ThomasVanNuffel/Iron-Solo-Synthesizer/Practise Enterprise 1/Drawings/Balance amplifier.tif

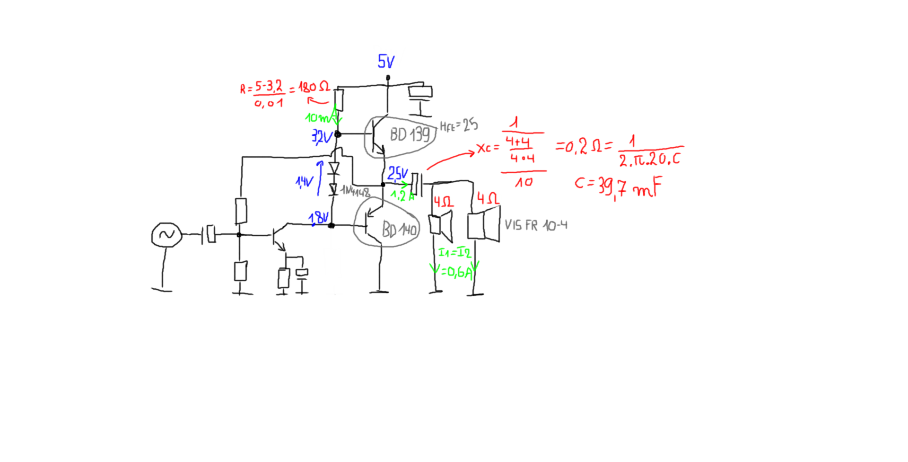
Practise Enterprise 1/Drawings/Balance amplifier.tif
