ThomasVanNuffel/Iron-Solo-Synthesizer/Practise Enterprise 1/Drawings/try.png

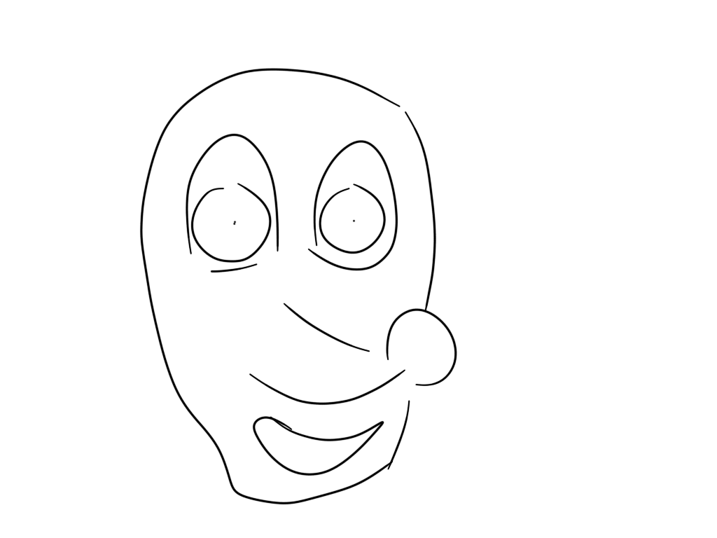
Practise Enterprise 1/Drawings/try.png
