ThomasVanNuffel/Iron-Solo-Synthesizer/Practise Enterprise 1/PCB/Nieuwe map/Envelope board.png

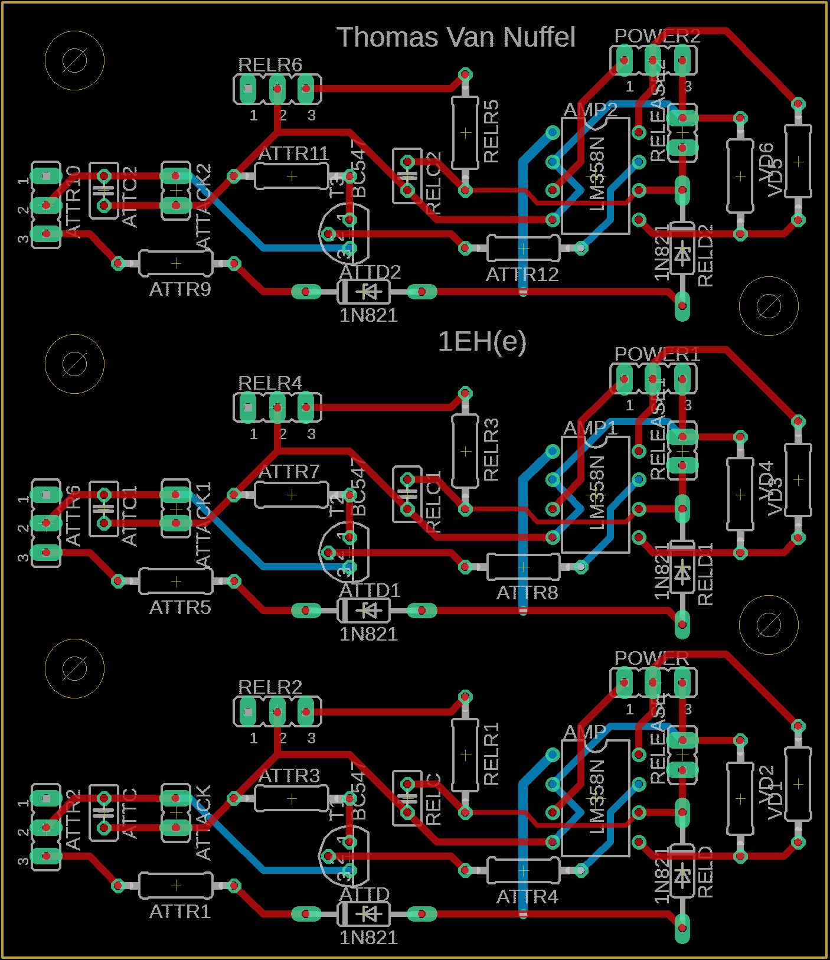
Practise Enterprise 1/PCB/Nieuwe map/Envelope board.png
