ThomasVanNuffel/Iron-Solo-Synthesizer/Practise Enterprise 1/PCB/Nieuwe map/Filter board.png

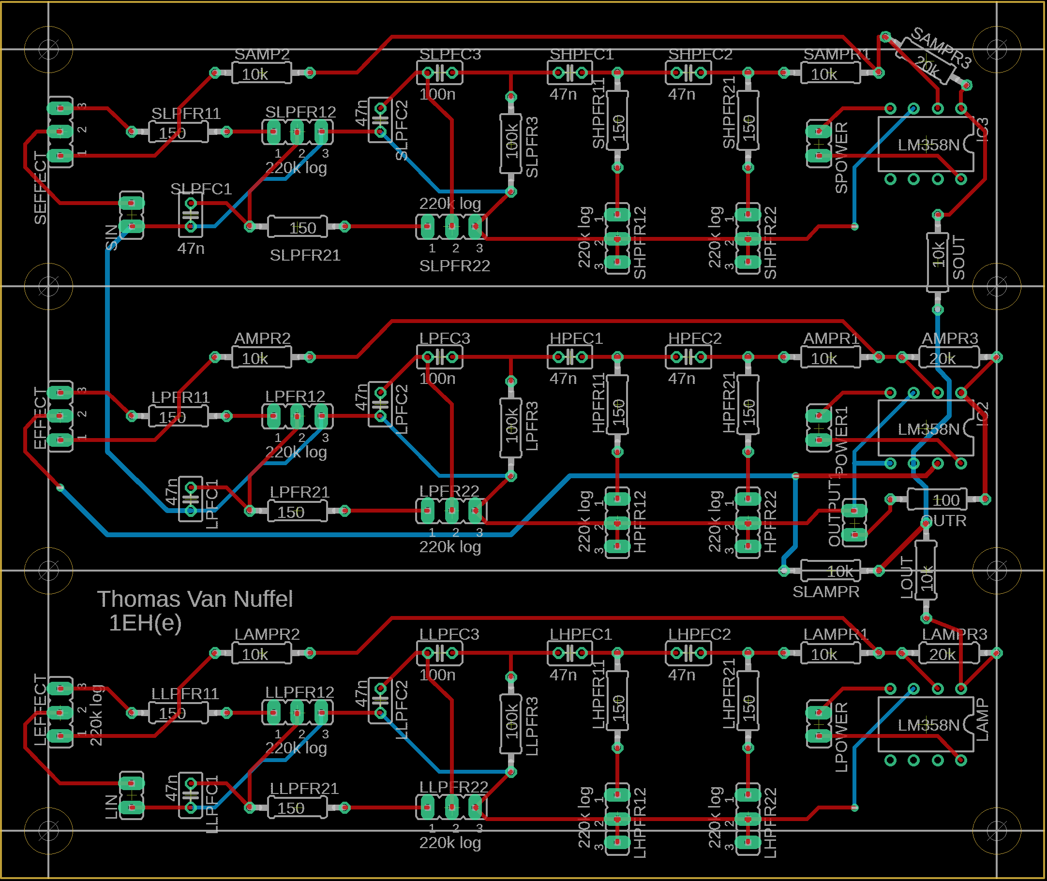
Practise Enterprise 1/PCB/Nieuwe map/Filter board.png
