ThomasVanNuffel/Iron-Solo-Synthesizer/Practise Enterprise 1/Design/EC11_rotary_encoder_knob.stp

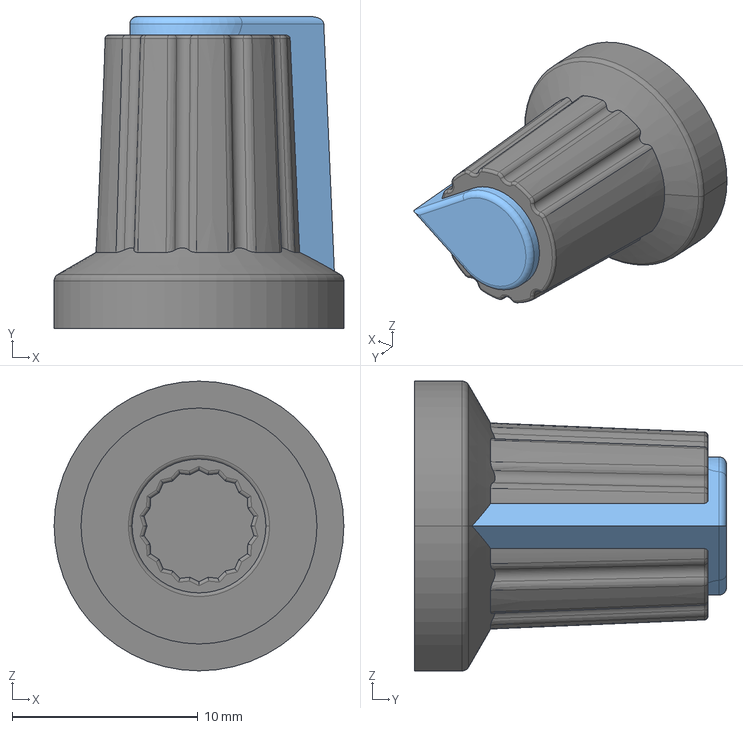
[picture p28: CAD file, 2021-11-29]
Practise Enterprise 1/Design/EC11_rotary_encoder_knob.stp
15.6 x 16.8 x 15.6 mm
