ThomasVanNuffel/Iron-Solo-Synthesizer/Practise Enterprise 1/Design/ground panel.SLDPRT

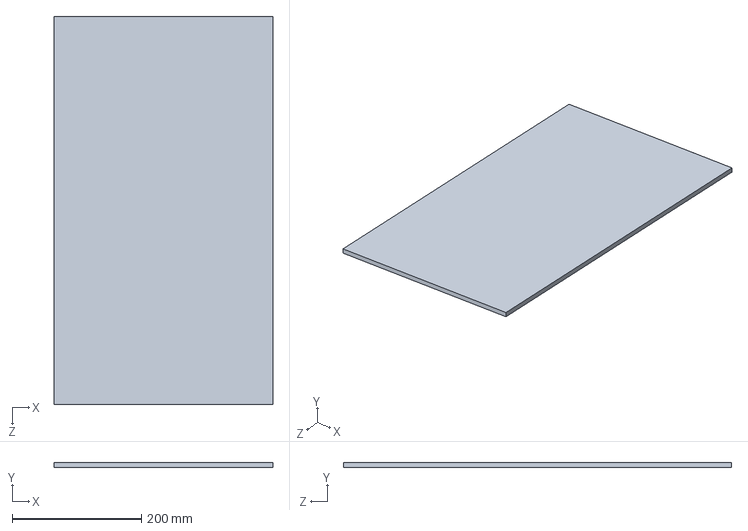
[picture p29: CAD file, 2021-11-29]
Practise Enterprise 1/Design/ground panel.SLDPRT
338.0 x 8.00 x 600.0 mm
