ThomasVanNuffel/Iron-Solo-Synthesizer/Practise Enterprise 1/Design/Part20.SLDPRT

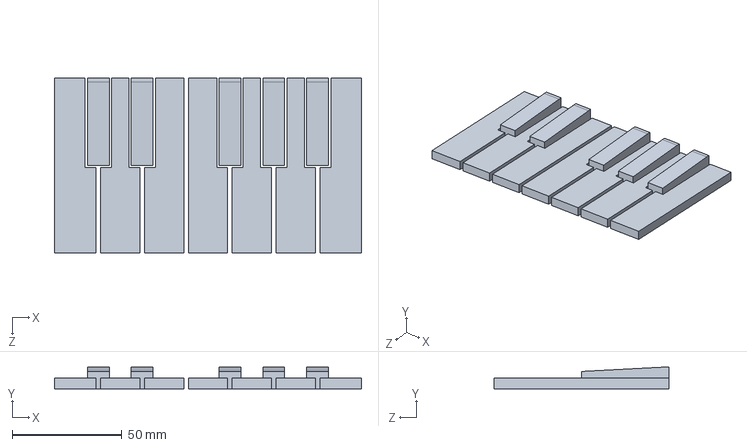
[picture p30: CAD file, 2021-11-29]
Practise Enterprise 1/Design/Part20.SLDPRT
140.0 x 10.0 x 80.0 mm
