ThomasVanNuffel/Iron-Solo-Synthesizer/Practise Enterprise 1/Design/RS-209-gold.step

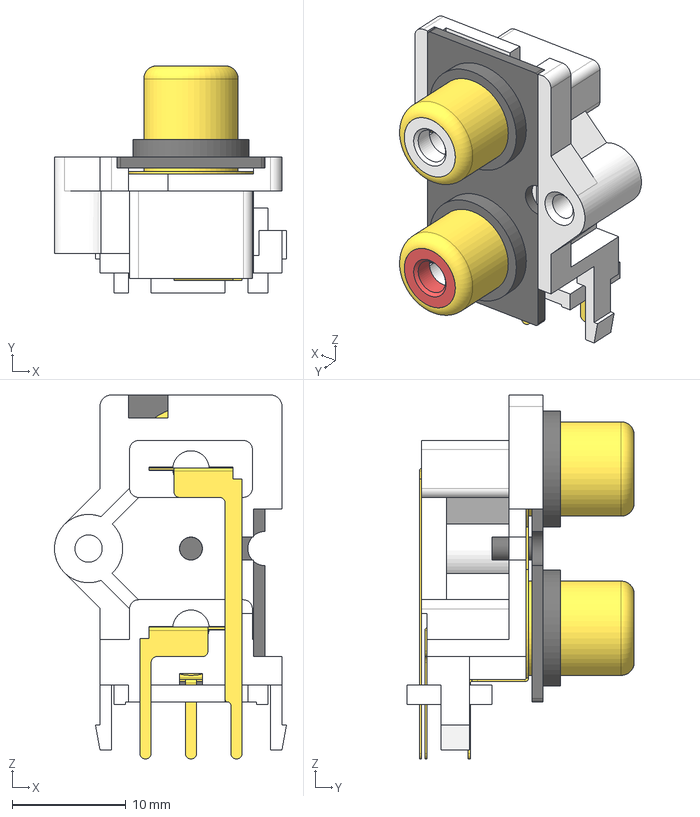
[picture p31: CAD file, 2021-11-29]
Practise Enterprise 1/Design/RS-209-gold.step
20.4 x 20.0 x 32.0 mm
