ThomasVanNuffel/Iron-Solo-Synthesizer/Practise Enterprise 1/Design/EG1249.step

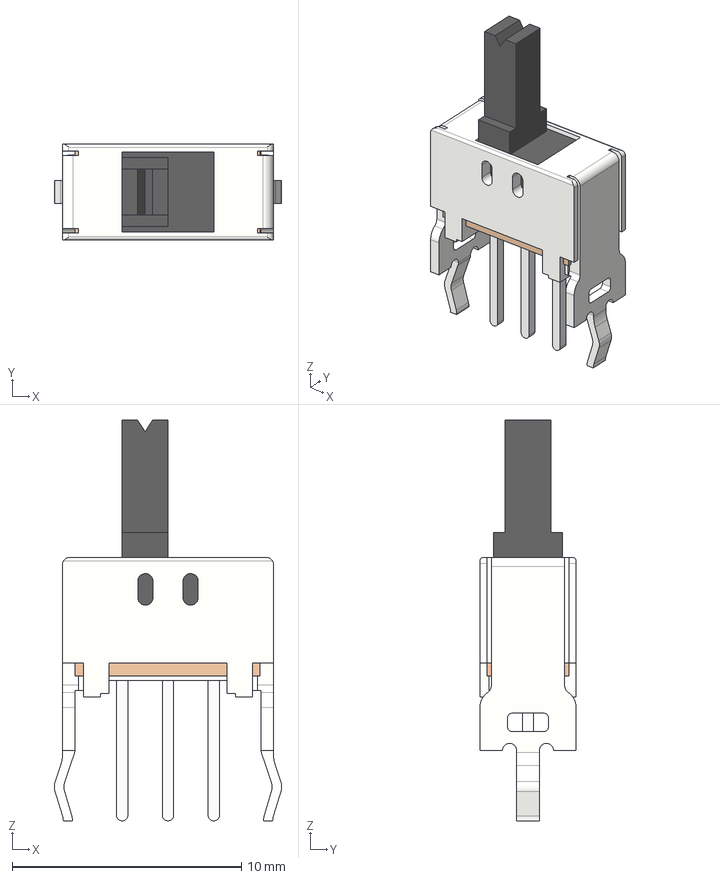
[picture p32: CAD file, 2021-11-29]
Practise Enterprise 1/Design/EG1249.step
9.93 x 4.20 x 17.5 mm
