ThomasVanNuffel/Iron-Solo-Synthesizer/Practise Enterprise 1/Design/front panel.SLDPRT

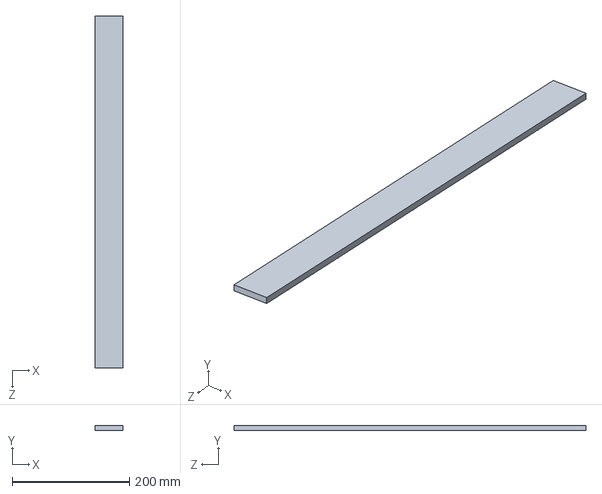
[picture p33: CAD file, 2021-11-29]
Practise Enterprise 1/Design/front panel.SLDPRT
48.0 x 8.00 x 600.0 mm
