ThomasVanNuffel/Iron-Solo-Synthesizer/Practise Enterprise 1/Design/ST-215N-01.step

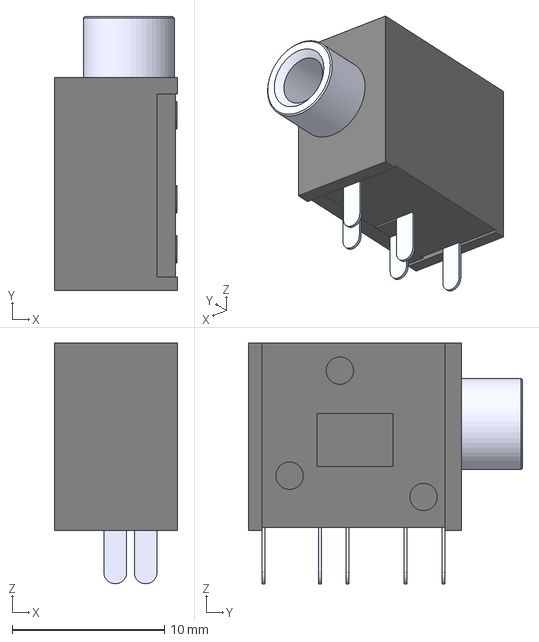
[picture p34: CAD file, 2021-11-29]
Practise Enterprise 1/Design/ST-215N-01.step
8.10 x 18.0 x 15.8 mm
