ThomasVanNuffel/Iron-Solo-Synthesizer/Practise Enterprise 1/Design/back panel.SLDPRT

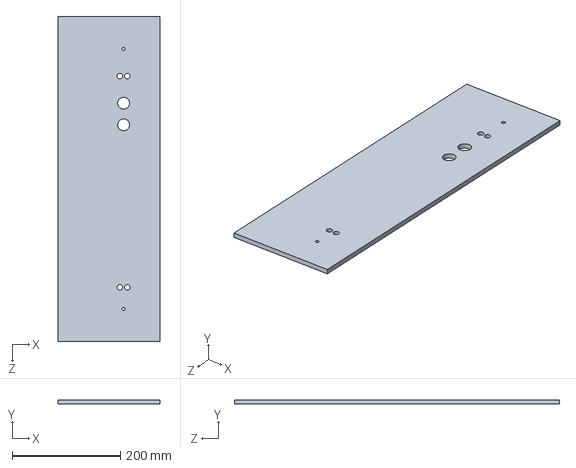
[picture p35: CAD file, 2021-11-29]
Practise Enterprise 1/Design/back panel.SLDPRT
188.0 x 8.00 x 600.0 mm
