ThomasVanNuffel/Iron-Solo-Synthesizer/Practise Enterprise 1/Design/bigpotje.STEP

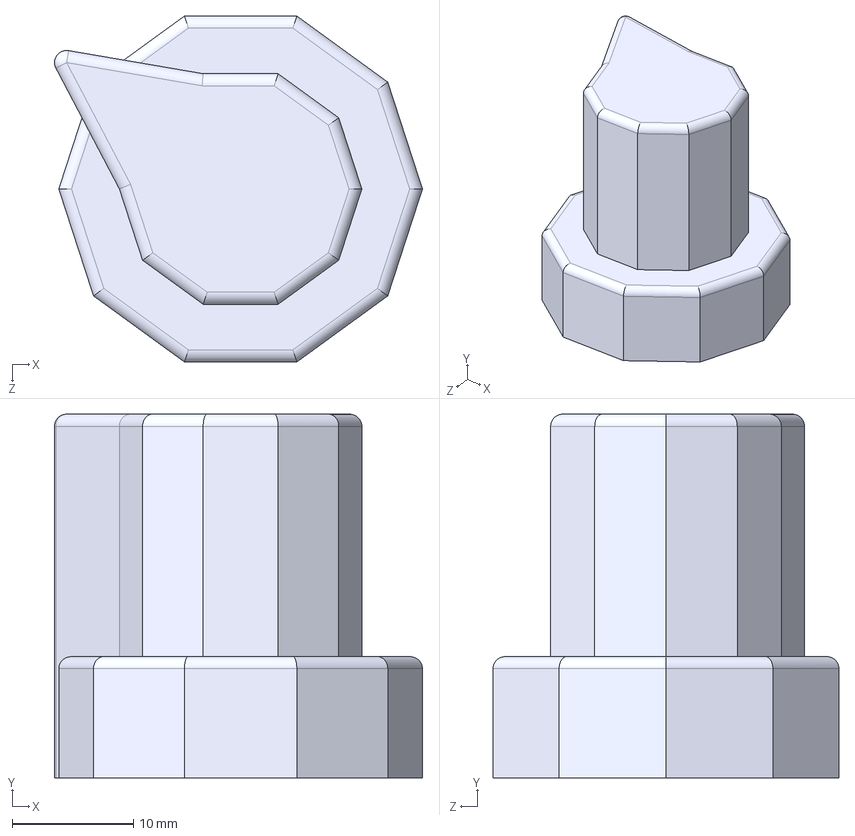
[picture p36: CAD file, 2021-11-29]
Practise Enterprise 1/Design/bigpotje.STEP
30.4 x 30.0 x 28.5 mm
