ThomasVanNuffel/Iron-Solo-Synthesizer/Practise Enterprise 1/Design/LED.SLDPRT

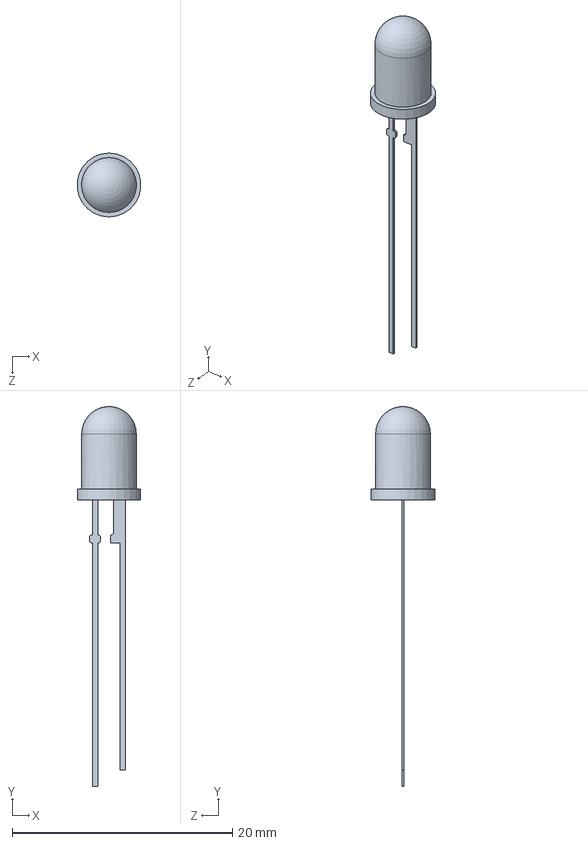
[picture p37: CAD file, 2021-11-29]
Practise Enterprise 1/Design/LED.SLDPRT
5.76 x 34.5 x 5.80 mm
