ThomasVanNuffel/Iron-Solo-Synthesizer/Practise Enterprise 1/Design/Momentary Push Button Switch.stp

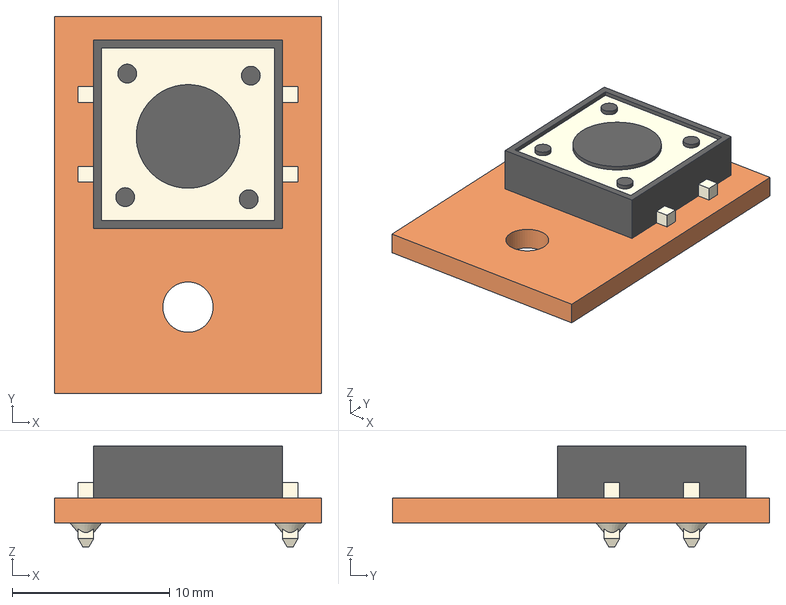
[picture p38: CAD file, 2021-11-29]
Practise Enterprise 1/Design/Momentary Push Button Switch.stp
17.0 x 24.0 x 6.40 mm
