ThomasVanNuffel/Iron-Solo-Synthesizer/Practise Enterprise 1/Design/Big pot.SLDPRT

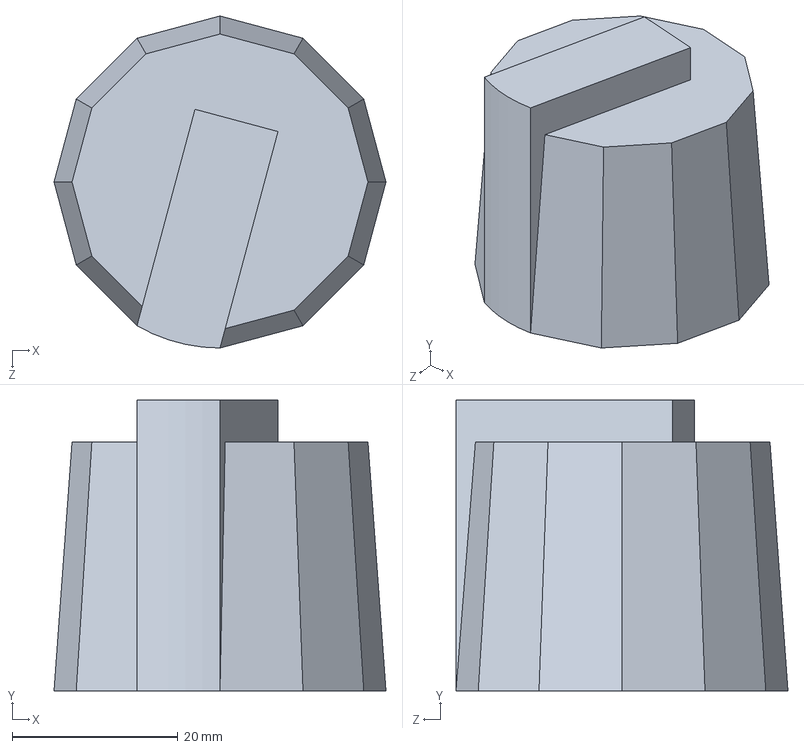
[picture p39: CAD file, 2021-11-29]
Practise Enterprise 1/Design/Big pot.SLDPRT
40.0 x 35.0 x 40.0 mm
