ThomasVanNuffel/Iron-Solo-Synthesizer/Practise Enterprise 1/Design/potdop.STEP

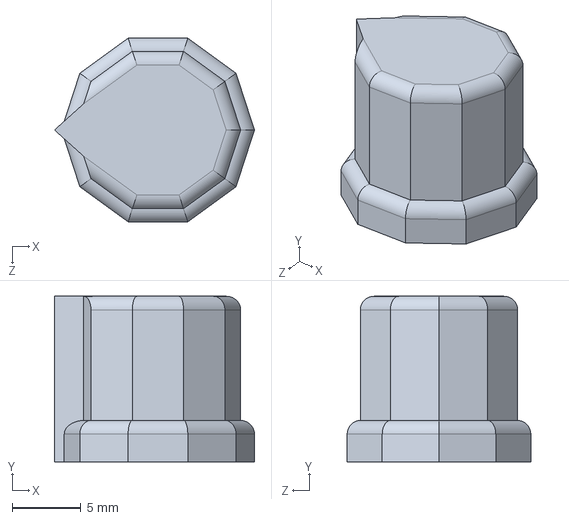
[picture p40: CAD file, 2021-11-29]
Practise Enterprise 1/Design/potdop.STEP
14.5 x 12.0 x 13.3 mm
