ThomasVanNuffel/Iron-Solo-Synthesizer/Practise Enterprise 1/Design/led panel.SLDPRT

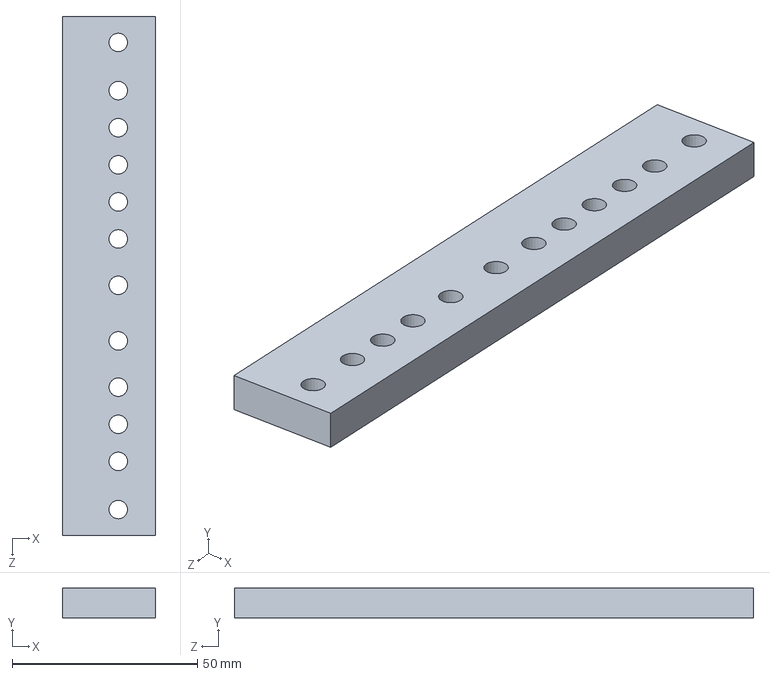
[picture p41: CAD file, 2021-11-29]
Practise Enterprise 1/Design/led panel.SLDPRT
25.0 x 8.00 x 140.0 mm
