ThomasVanNuffel/Iron-Solo-Synthesizer/Practise Enterprise 1/Design/MicroSwitch6mm.STEP

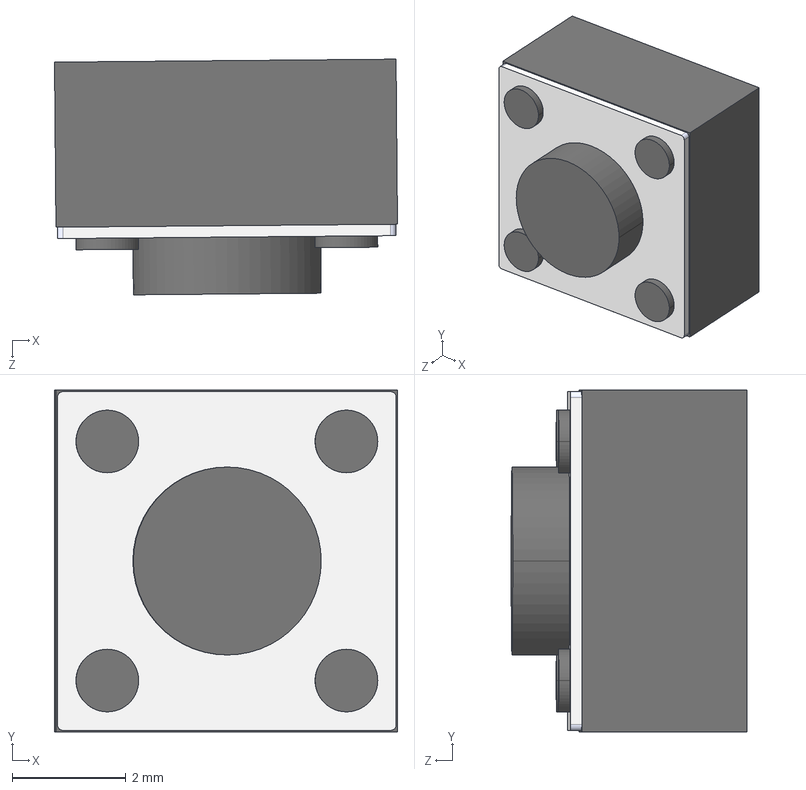
[picture p42: CAD file, 2021-11-29]
Practise Enterprise 1/Design/MicroSwitch6mm.STEP
6.03 x 6.00 x 4.14 mm
