ThomasVanNuffel/Iron-Solo-Synthesizer/Practise Enterprise 1/PCB/Three filters.brd

## EAGLE design Practise Enterprise 1/PCB/Three filters.brd (2021-11-29)

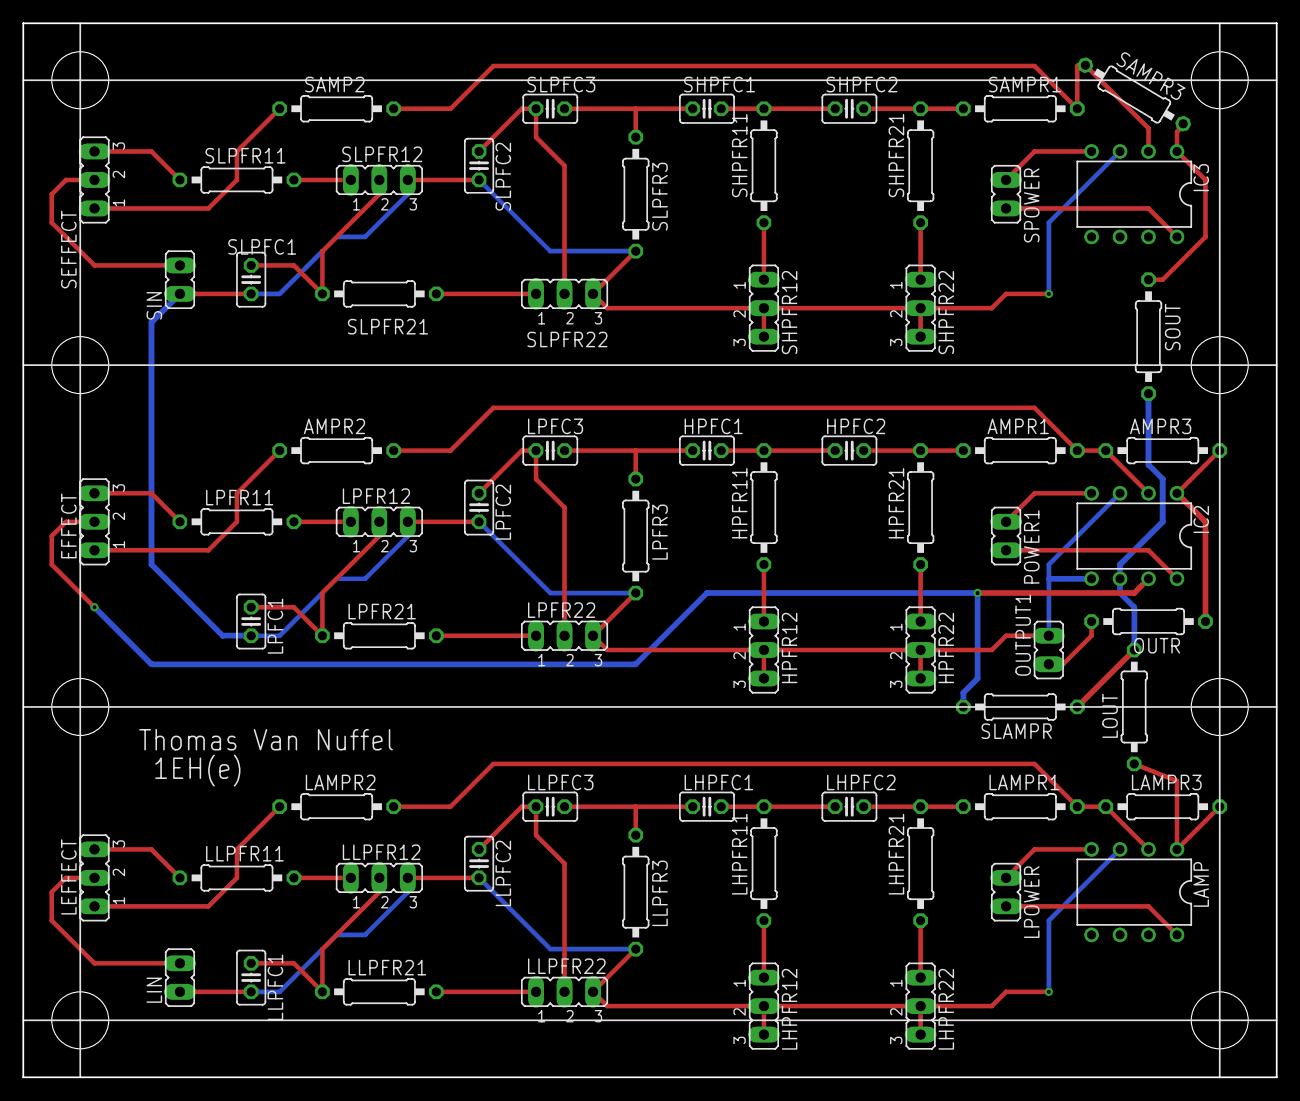
[picture p74: board Three filters.brd from above]

Board: 2 copper layers, 111.8 x 94.0 mm, 67 parts (0 on the bottom side), 52 nets.

Parts:
AMPR1, AMPR2: 10k; 0207/10
AMPR3: 20k; 0207/10
EFFECT: 220k log; JP2
HPFC1, HPFC2: 47n; C025-025X050
HPFR11, HPFR21: 150; 0207/10
HPFR12, HPFR22: 220k log; JP2
IC2, IC3: LM358N; DIL08
LAMP: LM358N; DIL08
LAMPR1, LAMPR2: 10k; 0207/10
LAMPR3: 20k; 0207/10
LEFFECT: 220k log; JP2
LHPFC1, LHPFC2: 47n; C025-025X050
LHPFR11, LHPFR21: 150; 0207/10
LHPFR12, LHPFR22: 220k log; JP2
LIN: JP1
LLPFC1, LLPFC2: 47n; C025-025X050
LLPFC3: 100n; C025-025X050
LLPFR3: 100k; 0207/10
LLPFR11, LLPFR21: 150; 0207/10
LLPFR12, LLPFR22: 220k log; JP2
LOUT: 10k; 0207/10
LPFC1, LPFC2: 47n; C025-025X050
LPFC3: 100n; C025-025X050
LPFR3: 100k; 0207/10
LPFR11, LPFR21: 150; 0207/10
LPFR12, LPFR22: 220k log; JP2
LPOWER: JP1
OUTPUT1: JP1
OUTR: 100; 0207/10
POWER1: JP1
SAMP2: 10k; 0207/10
SAMPR1: 10k; 0207/10
SAMPR3: 20k; 0207/10
SEFFECT: 220k log; JP2
SHPFC1, SHPFC2: 47n; C025-025X050
SHPFR11, SHPFR21: 150; 0207/10
SHPFR12, SHPFR22: 220k log; JP2
SIN: JP1
SLAMPR: 10k; 0207/10
SLPFC1, SLPFC2: 47n; C025-025X050
SLPFC3: 100n; C025-025X050
SLPFR3: 100k; 0207/10
SLPFR11, SLPFR21: 150; 0207/10
SLPFR12, SLPFR22: 220k log; JP2
SOUT: 10k; 0207/10
SPOWER: JP1

Connections:
unnamed: LLPFR11.2, LLPFR12.1
unnamed: LLPFC1.1, LLPFR12.2, LLPFR21.1
unnamed: LLPFC2.1, LLPFC3.1, LLPFR22.2
unnamed: LAMP.3, LHPFR12.2, LHPFR12.3, LHPFR22.2, LHPFR22.3, LIN.1, LLPFC1.2, LLPFC2.2, LLPFR3.2, LLPFR12.3, LLPFR22.3
unnamed: LEFFECT.3, LLPFR11.1
unnamed: LHPFC1.2, LHPFC2.1, LHPFR11.2
unnamed: LPFR11.2, LPFR12.1
unnamed: LAMP.1, LAMPR3.2, LOUT.1
unnamed: LAMP.8, LPOWER.2
unnamed: LAMP.4, LPOWER.1
unnamed: LAMPR2.1, LEFFECT.1
unnamed: LLPFR21.2, LLPFR22.1
unnamed: LHPFR21.1, LHPFR22.1
unnamed: LAMPR1.1, LHPFC2.2, LHPFR21.2
unnamed: LHPFR11.1, LHPFR12.1
unnamed: LPFC1.1, LPFR12.2, LPFR21.1
unnamed: LPFC2.1, LPFC3.1, LPFR22.2
unnamed: LHPFC1.1, LLPFC3.2, LLPFR3.1
unnamed: LEFFECT.2, LIN.2
unnamed: LAMP.2, LAMPR1.2, LAMPR2.2, LAMPR3.1
unnamed: HPFC1.2, HPFC2.1, HPFR11.2
unnamed: IC2.8, POWER1.2
unnamed: IC2.4, POWER1.1
unnamed: OUTPUT1.1, OUTR.2
unnamed: LPFR21.2, LPFR22.1
unnamed: AMPR1.1, HPFC2.2, HPFR21.2
unnamed: HPFR21.1, HPFR22.1
unnamed: HPFR11.1, HPFR12.1
unnamed: HPFC1.1, LPFC3.2, LPFR3.1
unnamed: EFFECT.2, IC2.7, SLAMPR.2
unnamed: AMPR1.2, AMPR2.2, AMPR3.1, IC2.2
unnamed: AMPR2.1, EFFECT.1
unnamed: EFFECT.3, LPFR11.1
unnamed: SLPFR11.2, SLPFR12.1
unnamed: SLPFC1.1, SLPFR12.2, SLPFR21.1
unnamed: SLPFC2.1, SLPFC3.1, SLPFR22.2
unnamed: HPFR12.2, HPFR12.3, HPFR22.2, HPFR22.3, IC2.3, IC2.5, IC3.3, LPFC1.2, LPFC2.2, LPFR3.2, LPFR12.3, LPFR22.3, OUTPUT1.2, SHPFR12.2, SHPFR12.3, SHPFR22.2, SHPFR22.3, SIN.1, SLPFC1.2, SLPFC2.2, SLPFR3.2, SLPFR12.3, SLPFR22.3
unnamed: SHPFC1.2, SHPFC2.1, SHPFR11.2
unnamed: IC3.8, SPOWER.2
unnamed: IC3.4, SPOWER.1
unnamed: IC3.1, SAMPR3.2, SOUT.1
unnamed: SLPFR21.2, SLPFR22.1
unnamed: SAMPR1.1, SHPFC2.2, SHPFR21.2
unnamed: SHPFR21.1, SHPFR22.1
unnamed: SHPFR11.1, SHPFR12.1
unnamed: SHPFC1.1, SLPFC3.2, SLPFR3.1
unnamed: SEFFECT.2, SIN.2
unnamed: IC3.2, SAMP2.2, SAMPR1.2, SAMPR3.1
unnamed: SAMP2.1, SEFFECT.1
unnamed: SEFFECT.3, SLPFR11.1
S$1: IC2.6, LOUT.2, SLAMPR.1, SOUT.2
S$2: AMPR3.2, IC2.1, OUTR.1
